bot190/MPPT/Software/sweep.c

/******************************************************************************
 *                    Maximum Power Point Tracker (MPPT)
 *
 * This file implements the sweep method of finding and staying at the MPPT.
 *
 * This project is in fulfillment of the Major Qualifying Project at
 * Worcester Polytechnic Institute.
 *
 * Authored by:
 * 	Jonathan Adams
 * 	Ben Beauregard
 * 	Andrew Flynn
 *
 *****************************************************************************/

// Includes
#include "main.h"
#include "sweep.h"
#include "msp430.h"


int sweep(volatile char *DCTL) {

    if (periodic_timer_count >= SWEEP_INTERVAL) {
        // Reset timer and sweep again
        periodic_timer_count = 0;
        sweep_reset(DCTL);
    }
    // Only need to do something if sweep is not complete
    if (sweep_complete == 0 ) {
        power = (long) i_mppt * v_mppt;
        // New power > old power, save duty cycle
        if (power > max_power) {
            max_power_duty_cycle = mppt_duty_cycle;
            max_power = power;
        }
        // We've reached 100% duty cycle, mark as complete,
        // Set duty cycle to maximum power point
        if (mppt_duty_cycle == 320) {
            sweep_complete = 1;
            mppt_duty_cycle = max_power_duty_cycle;
        } else {
            // Haven't completed sweep yet, increment duty cycle
            mppt_duty_cycle += SWEEPINC;
            /* TESTING CODE */
            if (mppt_duty_cycle % 16 == 0) {
                // Turn on LED at P1.6 every 5% duty cycle
                P1OUT |= (BIT6);
            } else {
                // Turn off LED at P1.6 on next cycle
                P1OUT &= (~BIT6);
            }
            /* TESTING CODE */
        }
    }
    return mppt_duty_cycle;
}

/** \brief Sweep reset called when button is pushed
 *
 * Function handles restarting sweep, including resetting variables
 */
void sweep_reset(volatile char *DCTL) {
    max_power = 0;
    mppt_duty_cycle=80;
    sweep_complete = 0;
}
